abhijithabhiakl/Redragon_K617-QMK_port/Redragon_K617.kicad_pcb

## KiCad design Foot_Switch.kicad_sch

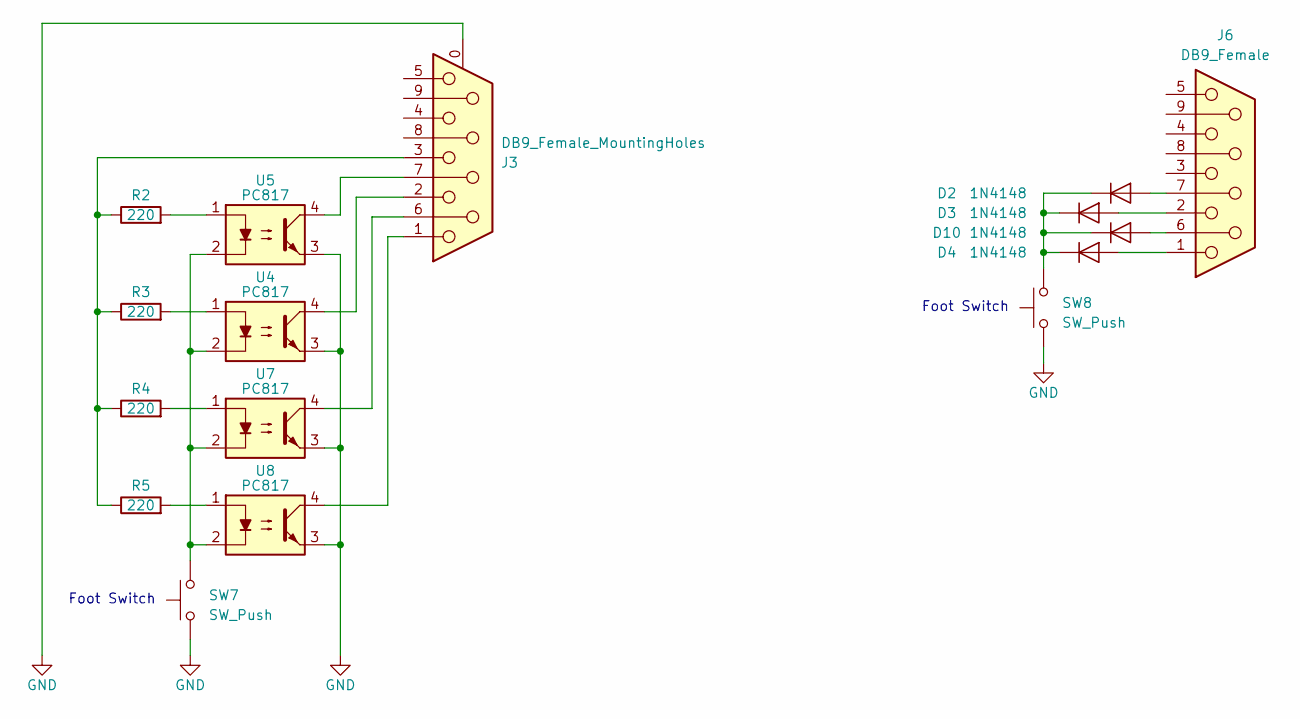
[picture p5: schematic Foot_Switch.kicad_sch]

Parts:
D2, D3, D4, D10: 1N4148; D_DO-35_SOD27_Horizontal_RM10
J3: DB9_Female_MountingHoles
J6: DB9_Female
R2, R3, R4, R5: 220
SW7, SW8: SW_Push
U4, U5, U7, U8: PC817; DIP-4_W7.62mm

Connections:
GND: J3.0 (PAD), SW7.1, SW8.1, U4.3, U5.3, U7.3, U8.3
unnamed: D2.2 (A), J6.7
unnamed: D3.2 (A), J6.2
unnamed: D4.2 (A), J6.1
unnamed: D2.1 (K), D3.1 (K), D4.1 (K), D10.1 (K), SW8.2
unnamed: D10.2 (A), J6.6
unnamed: J3.1, U8.4
unnamed: J3.2, U4.4
unnamed: J3.3, R2.1, R3.1, R4.1, R5.1
unnamed: J3.6, U7.4
unnamed: J3.7, U5.4
unnamed: R2.2, U5.1
unnamed: R3.2, U4.1
unnamed: R4.2, U7.1
unnamed: R5.2, U8.1
unnamed: SW7.2, U4.2, U5.2, U7.2, U8.2

Notes on the sheet:
Foot Switch
