abhijithabhiakl/Redragon_K617-QMK_port/Redragon_K617.kicad_pcb

## KiCad design LEDs_Drivers.kicad_sch

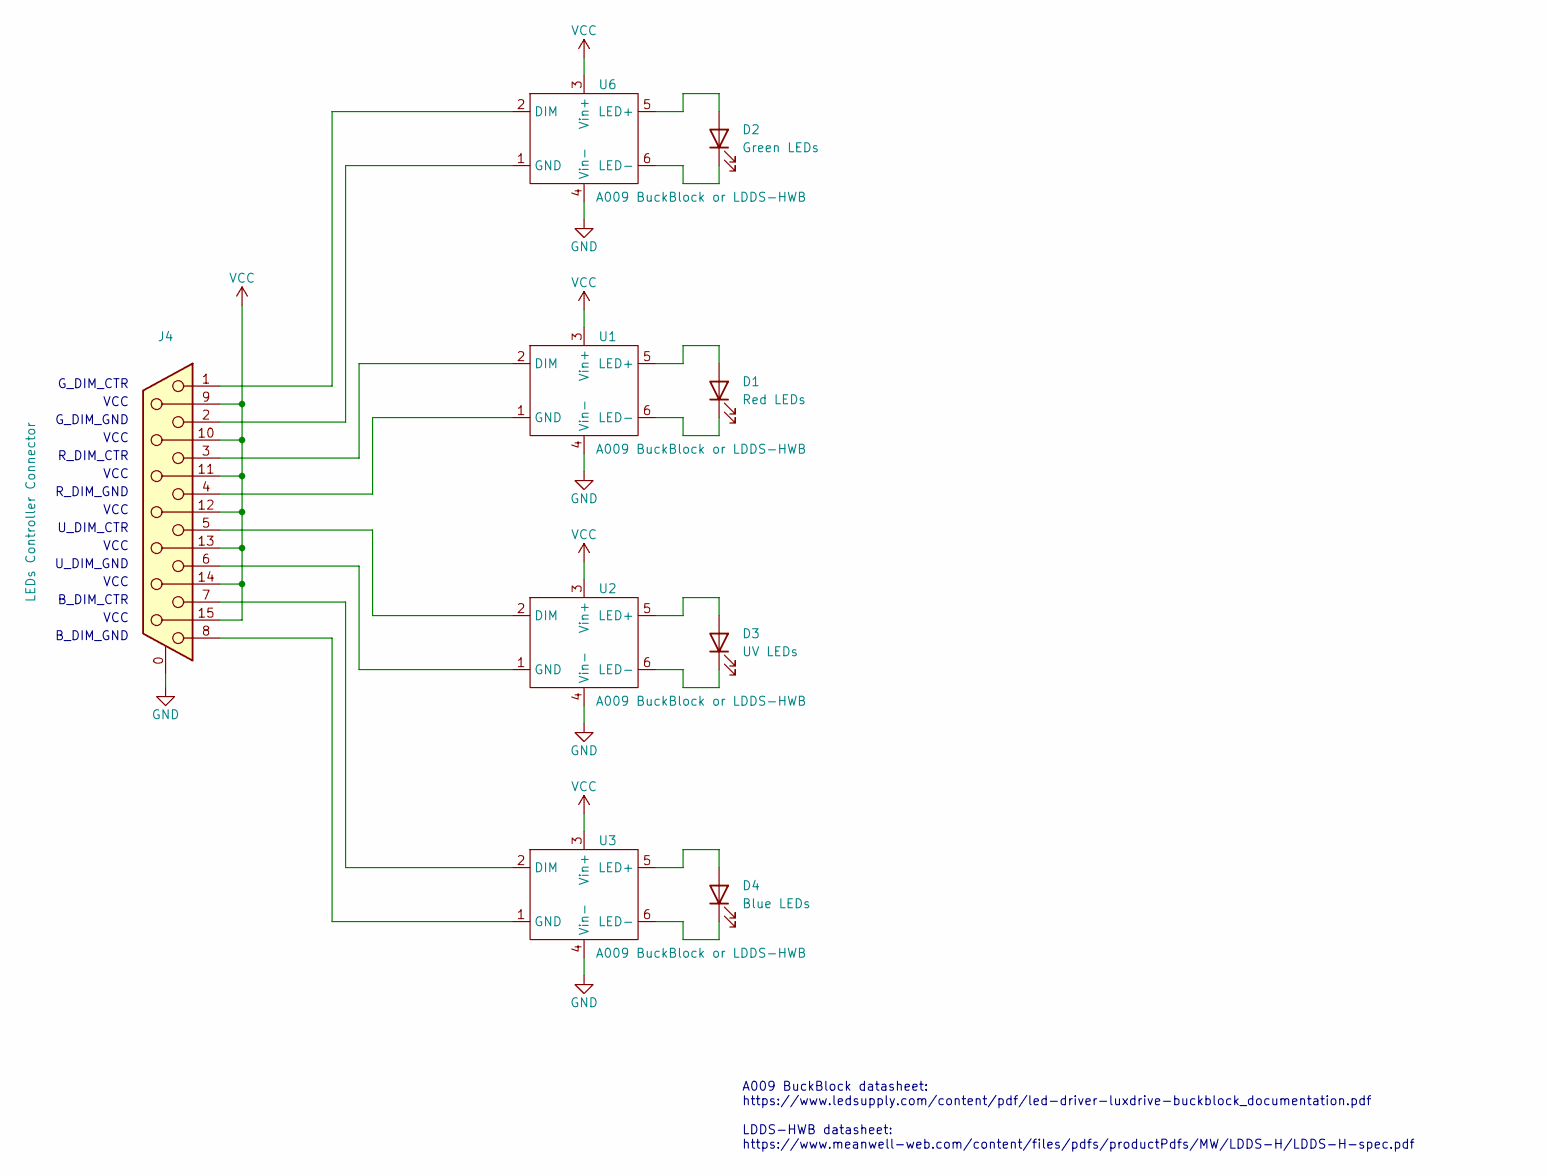
[picture p7: schematic LEDs_Drivers.kicad_sch]

Parts:
D1: Red LEDs
D2: Green LEDs
D3: UV LEDs
D4: Blue LEDs
J4: LEDs Controller Connector
U1, U2, U3, U6: A009 BuckBlock or LDDS-HWB

Connections:
GND: J4.0 (PAD), U1.4 (Vin-), U2.4 (Vin-), U3.4 (Vin-), U6.4 (Vin-)
unnamed: D1.1 (K), U1.6 (LED-)
unnamed: D1.2 (A), U1.5 (LED+)
unnamed: D2.1 (K), U6.6 (LED-)
unnamed: D2.2 (A), U6.5 (LED+)
unnamed: D3.1 (K), U2.6 (LED-)
unnamed: D3.2 (A), U2.5 (LED+)
unnamed: D4.1 (K), U3.6 (LED-)
unnamed: D4.2 (A), U3.5 (LED+)
unnamed: J4.1, U6.2 (DIM)
unnamed: J4.2, U6.1 (GND)
unnamed: J4.3, U1.2 (DIM)
unnamed: J4.4, U1.1 (GND)
unnamed: J4.5, U2.2 (DIM)
unnamed: J4.6, U2.1 (GND)
unnamed: J4.7, U3.2 (DIM)
unnamed: J4.8, U3.1 (GND)
VCC: J4.9, J4.10, J4.11 (P111), J4.12, J4.13, J4.14, J4.15, U1.3 (Vin+), U2.3 (Vin+), U3.3 (Vin+), U6.3 (Vin+)

Notes on the sheet:
G_DIM_CTR
U_DIM_CTR
VCC
G_DIM_GND
R_DIM_GND
B_DIM_CTR
U_DIM_GND
R_DIM_CTR
B_DIM_GND
A009 BuckBlock datasheet: https://www.ledsupply.com/content/pdf/led-driver-luxdrive-buckblock_documentation.pdf LDDS-HWB datasheet: https://www.meanwell-web.com/content/files/pdfs/productPdfs/MW/LDDS-H/LDDS-H-spec.pdf
