abhijithabhiakl/Redragon_K617-QMK_port/Redragon_K617.kicad_pcb

## KiCad design Power.kicad_sch

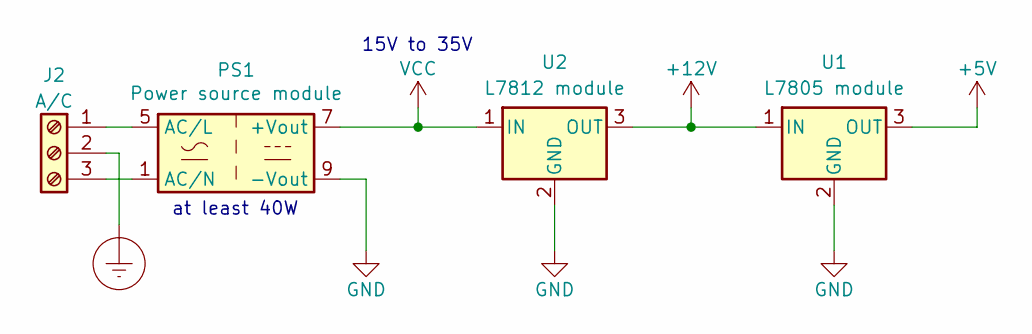
[picture p8: schematic Power.kicad_sch]

Parts:
J2: A/C
PS1: Power source module; Converter_ACDC_Hahn_HS-400xx_THT
U1: L7805 module
U2: L7812 module

Connections:
+5V: U1.3 (OUT)
+12V: U1.1 (IN), U2.3 (OUT)
Earth_Protective: J2.2
GND: PS1.9 (-Vout), U1.2 (GND), U2.2 (GND)
unnamed: J2.1, PS1.5 (AC/L)
unnamed: J2.3, PS1.1 (AC/N)
VCC: PS1.7 (+Vout), U2.1 (IN)

Notes on the sheet:
15V to 35V
at least 40W
