abhijithabhiakl/Redragon_K617-QMK_port/Redragon_K617.kicad_pcb

## KiCad design metronome.kicad_sch

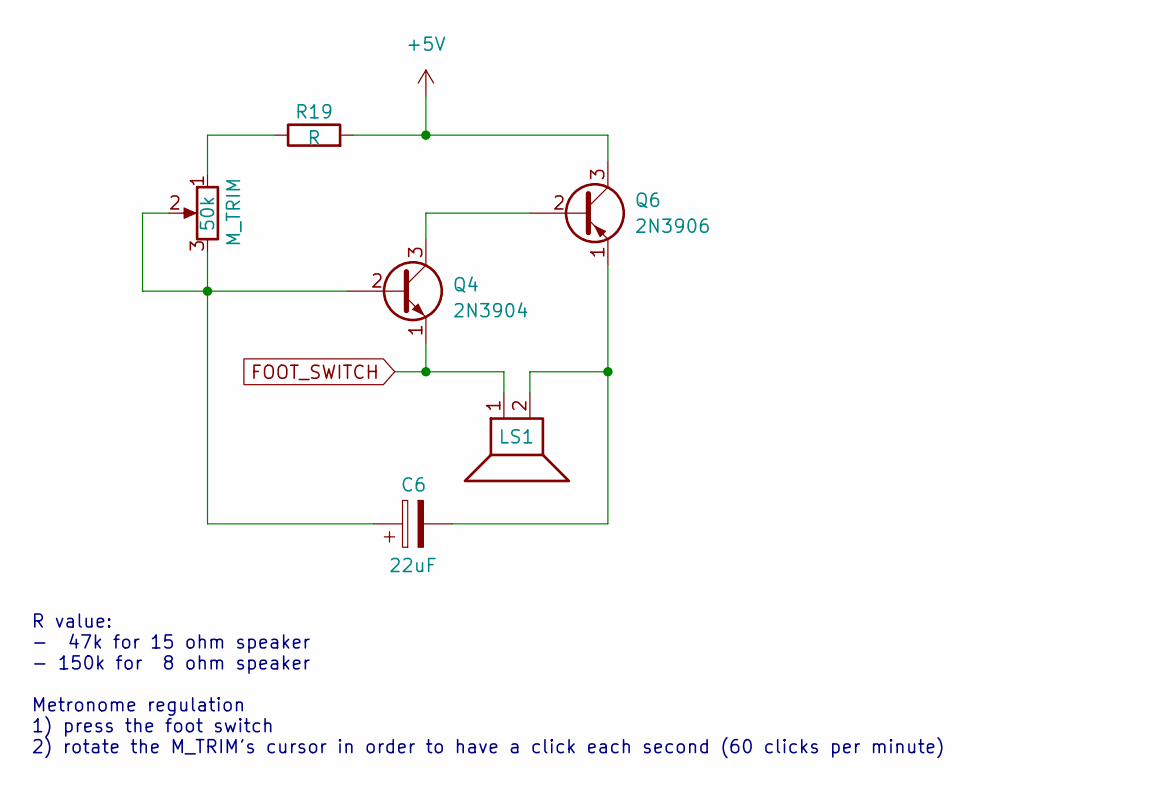
[picture p9: schematic metronome.kicad_sch]

Parts:
C6: 22uF
LS1: (no value)
M_TRIM: 50k
Q4: 2N3904; TO-92_Molded_Narrow
Q6: 2N3906; TO-92_Inline
R19: R

Connections:
+5V: Q6.3 (C), R19.2
FOOT_SWITCH: LS1.1, Q4.1 (E)
unnamed: C6.1, M_TRIM.2, M_TRIM.3, Q4.2 (B)
unnamed: C6.2, LS1.2, Q6.1 (E)
unnamed: M_TRIM.1, R19.1
unnamed: Q4.3 (C), Q6.2 (B)

Notes on the sheet:
R value: - 47k for 15 ohm speaker - 150k for 8 ohm speaker Metronome regulation 1) press the foot switch 2) rotate the M_TRIM's cursor in order to have a click each second (60 clicks per minute)
